denouche/led-o-clock/firmware/include/ota_service.h

#ifndef OTA_SERVICE_H
#define OTA_SERVICE_H

#include <Arduino.h>

struct FirmwareInfo {
    String latestVersion;
    String downloadUrl;
};

FirmwareInfo getLatestFirmwareInfo();
void updateFirmwareIfNeeded();

#endif
